Nagi-1010/Line-Following-Robot-with-Ball-Putting-Mechanism/fusion360_design/Front_View (With Ball-Putting Mechanism).jpeg

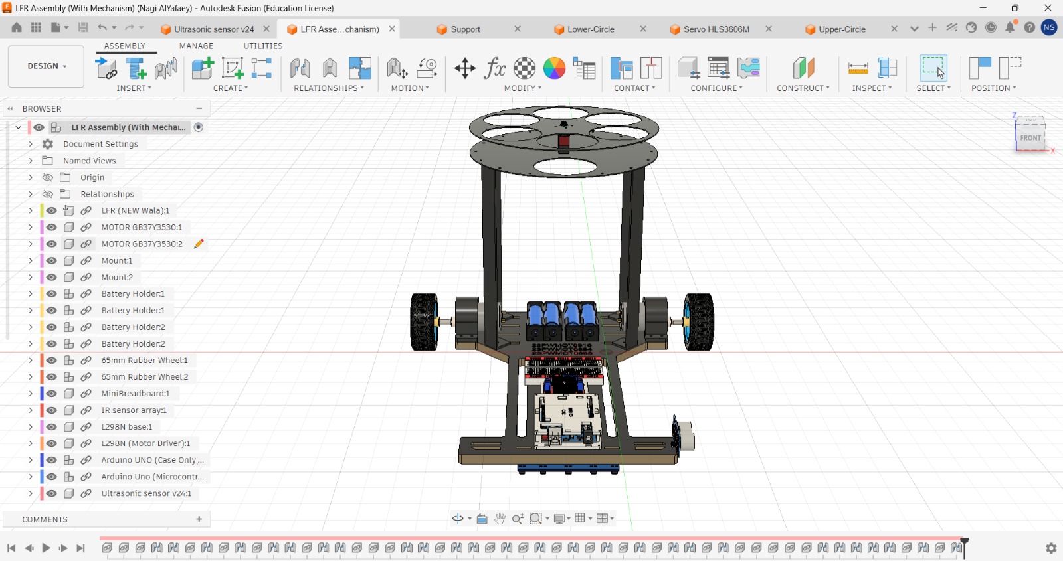
fusion360_design/Front_View (With Ball-Putting Mechanism).jpeg
