Nagi-1010/Line-Following-Robot-with-Ball-Putting-Mechanism/images/final_robot_side_view.jpeg

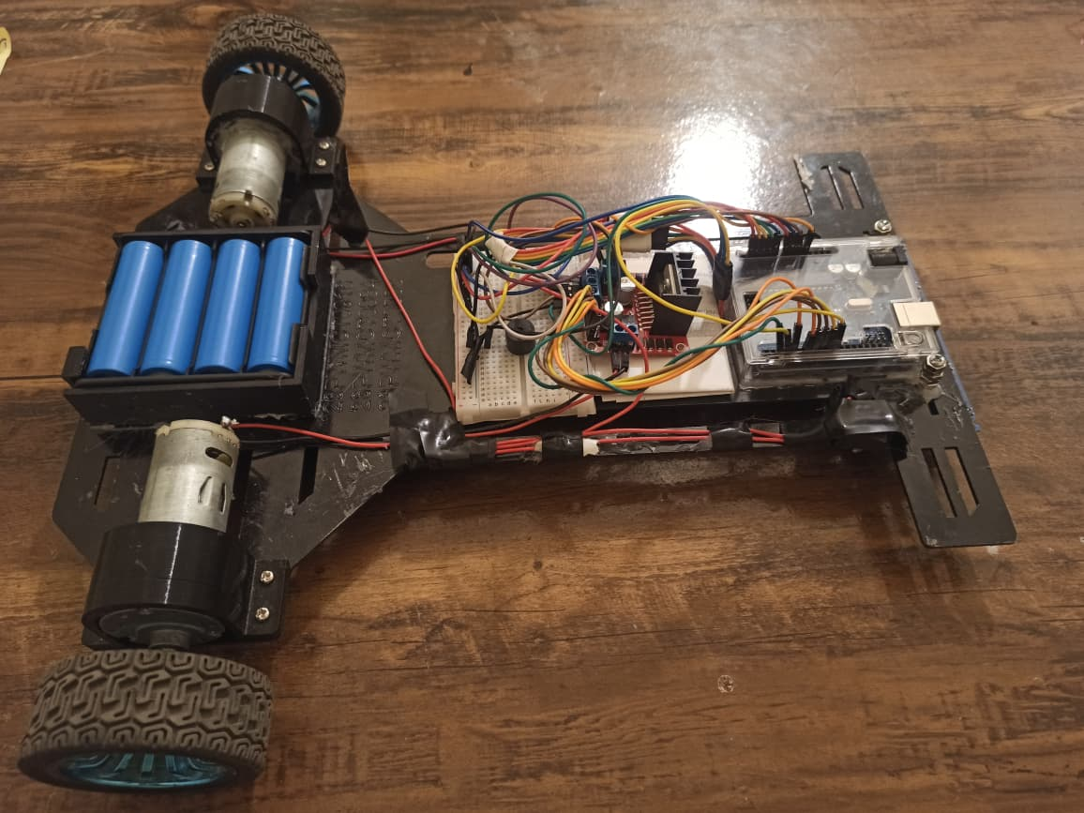
images/final_robot_side_view.jpeg
